aimeesimons/EEE3088F-Group-14/4. Miscellaneous files/BOMS/FullSchematic_Spreadsheet.xlsx

Component Count: | 58
Collated Components:
Item | Qty | Reference(s) | Value | JLCPCB Part # | Price | Price ( 1 board) | Price (5 boards)
1 | 1 | BT1 | Battery_Cell | C2988620 | $1.41 | $1.41 | $7.05
2 | 4 | C1, C2, C3, C4 | 100nF | C24497 | $0.08 | $0.32 | $1.60
3 | 4 | C8, C9, C10, C11 | 10uF | C1691 | $0.08 | $0.24 | $1.20
4 | 1 | C12 | C_Variable | C125363 | $0.31 | $0.31 | $1.54
5 | 1 | C13 | 100nF | C24497 | $0.08 | $0.32 | $1.60
6 | 3 | D1, D2, D3 | LED | N/A | $0,0139 | $0.04 | $0.21
7 | 1 | D4 | 1N5819 | C437199 | $0.02 | $0.02 | $0.08
8 | 1 | IC1 | TTP223E-BA6 | C1693666 | $0.10 | $0.10 | $0.50
9 | 1 | J1 | USB_B_Micro | C404969 | $0,0273 | $0.03 | $0.14
10 | 1 | J2 | TP4056 | C382139 | $0.11 | $0.11 | $0.55
11 | 1 | LEDcharge1 | RED | C2286 | $0.01 | $0.01 | $0.05
12 | 1 | P1 | Touch Pad | N/A | $0.00 | $0.00 | $0.00
13 | 1 | Q1 | PMOS | C115991 | $0.52 | $0.52 | $2.60
14 | 2 | Qrevpol1, Qrevpol2 | PMOS | C5337196 | $0.09 | $0.18 | $0.90
15 | 3 | R1, R2, R3 | 270 | C4466 | $0,0039 | $0.01 | $0.58
16 | 6 | R4, R5, R7, R15, R16, R17 | 0 | C17888 | $0.003 | $0.01 | $0.06
17 | 1 | R 6 | 4700 | C23162 | $0,0005 | $0.001 | $0.01
18 | 1 | R 10 | 1k | C4410 | $0.001 | $0.001 | $0.01
19 | 1 | R 11 | 180 | C22828 | $0.0017 | $0.0017 | $0.01
20 | 1 | R 12 | LDR03 | C125627 | $0.04 | $0.04 | $0.20
21 | 1 | R 13 | 2k | C17944 | $0.001 | $0.001 | $0.01
22 | 16 | TP1, TP2, TP3, TP4, TP6, TP7, TP8, TP9, TP10, TP11, TP12, TP13, TP14, TP15, TP16, TP19 | TestPoint | N/A | $0 | $0.00 | $0.00
23 | 1 | TP17 | TestPoint | N/A | $0.00 | $0.00 | $0.00
24 | 1 | U1 | LM1117-3.3 | C126027 | $0.07 | $0.07 | $0.36
25 | 1 | U2 | CH340C | C84681 | $0.47 | $0.47 | $2.35
26 | 1 | U3 | 24LC64 | C511260 | $0,5172 | $0.52 | $2.59
27 | 1 | U4 | STM32F051C6T6 | N/A | $0.00 | $0.00 | $0.00
 |  |  |  |  |  |  | $24.18
